euangoodbrand/IoT-Card-Shuffler/Documentation Resources/final_interface.png

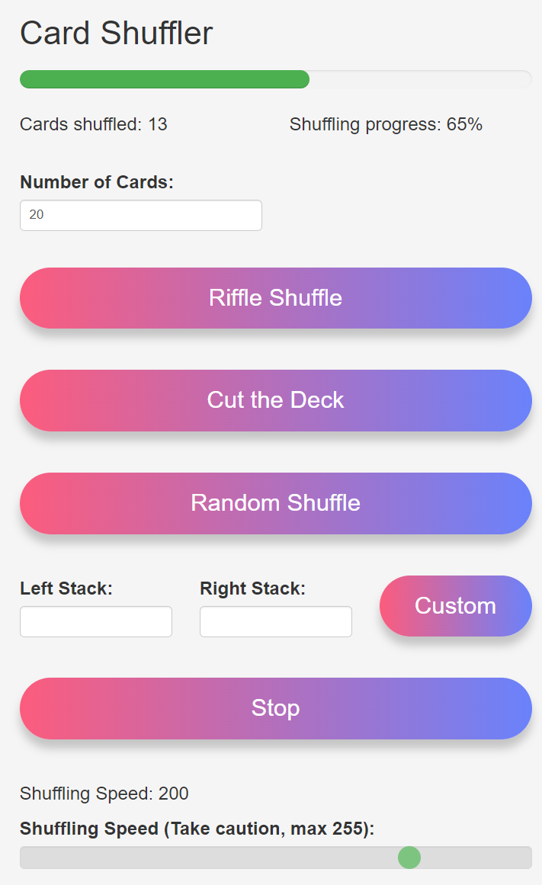
Documentation Resources/final_interface.png
