euangoodbrand/IoT-Card-Shuffler/Card Shuffler/3D Print Files/medium gear.stl

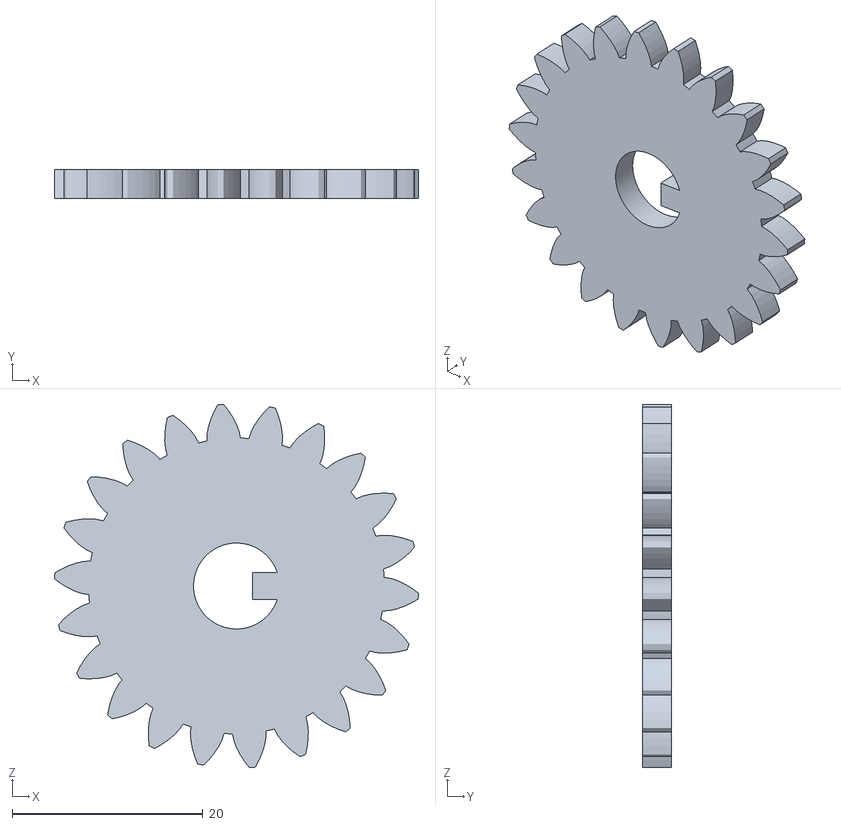
[picture p41: CAD file, 2023-05-23]
Card Shuffler/3D Print Files/medium gear.stl
38.2 x 3.00 x 38.1
