euangoodbrand/IoT-Card-Shuffler/Card Shuffler/3D Print Files/handle.stl

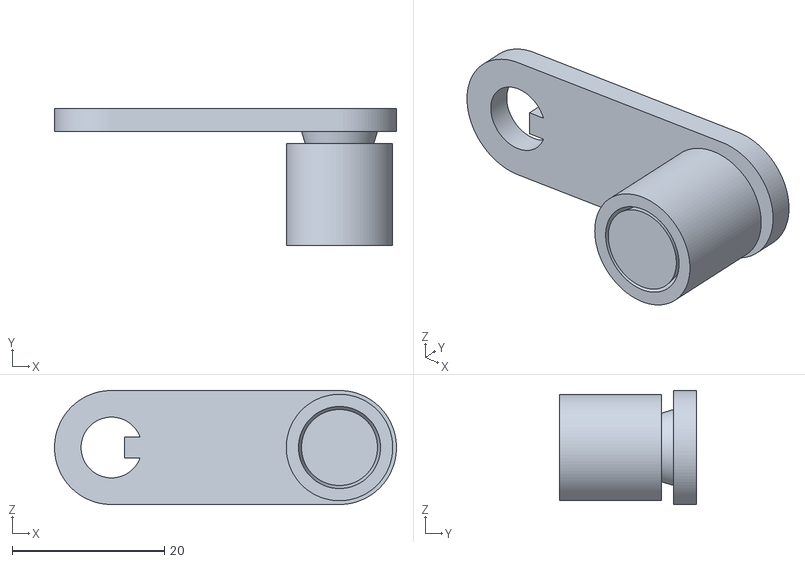
[picture p42: CAD file, 2023-05-23]
Card Shuffler/3D Print Files/handle.stl
45.0 x 18.0 x 15.0
