euangoodbrand/IoT-Card-Shuffler/Card Shuffler/3D Print Files/old right spacer.stl

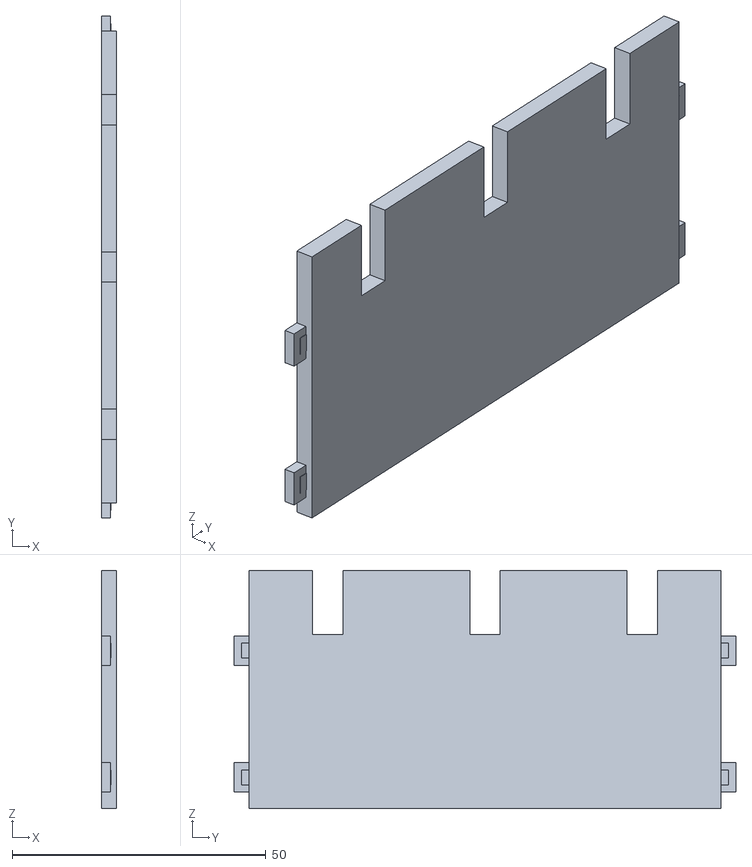
[picture p43: CAD file, 2023-05-23, an earlier design]
Card Shuffler/3D Print Files/old right spacer.stl
3.00 x 99.0 x 47.0
