euangoodbrand/IoT-Card-Shuffler/Card Shuffler/3D Print Files/shaft old design.stl

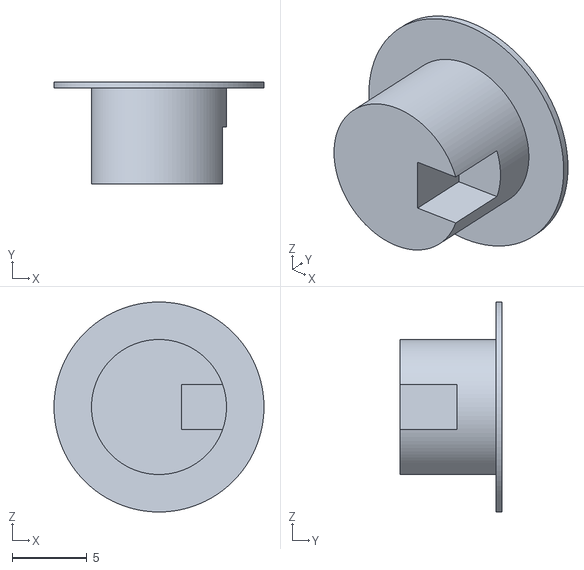
[picture p44: CAD file, 2023-05-23, an earlier design]
Card Shuffler/3D Print Files/shaft old design.stl
14.0 x 6.80 x 14.0
